kbhse/EnergyMonitor/KiCad/v1.1/images/17747-ESP-WROOM-32__16MB__ESP32_WiFi-BT-BLE_MCU_Module-01.jpg

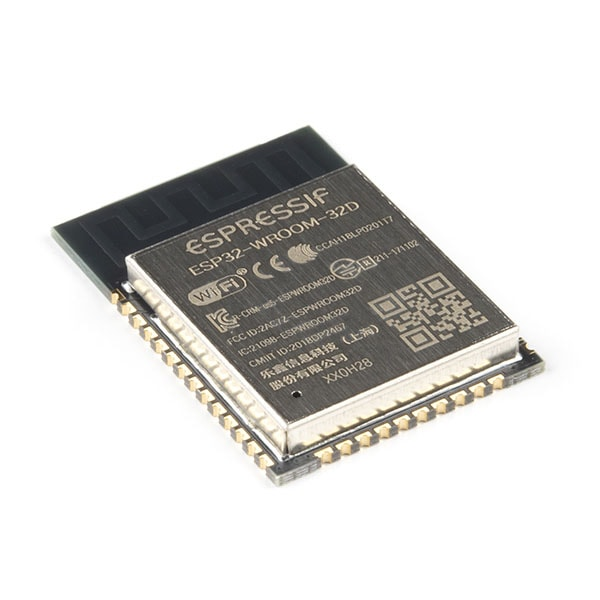
KiCad/v1.1/images/17747-ESP-WROOM-32__16MB__ESP32_WiFi-BT-BLE_MCU_Module-01.jpg
