kbhse/EnergyMonitor/KiCad/v1.1/images/ESP32_D1_MINI Footprint.PNG

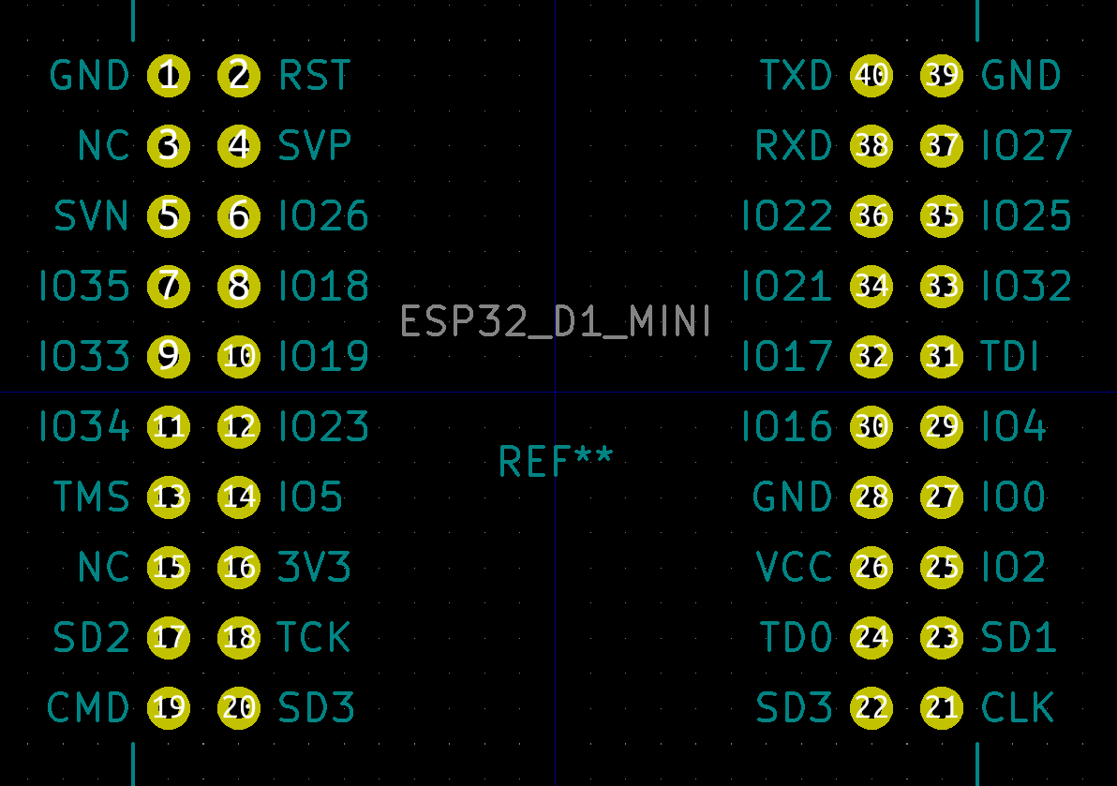
KiCad/v1.1/images/ESP32_D1_MINI Footprint.PNG
