kbhse/EnergyMonitor/Solidworks/images/case v01.png

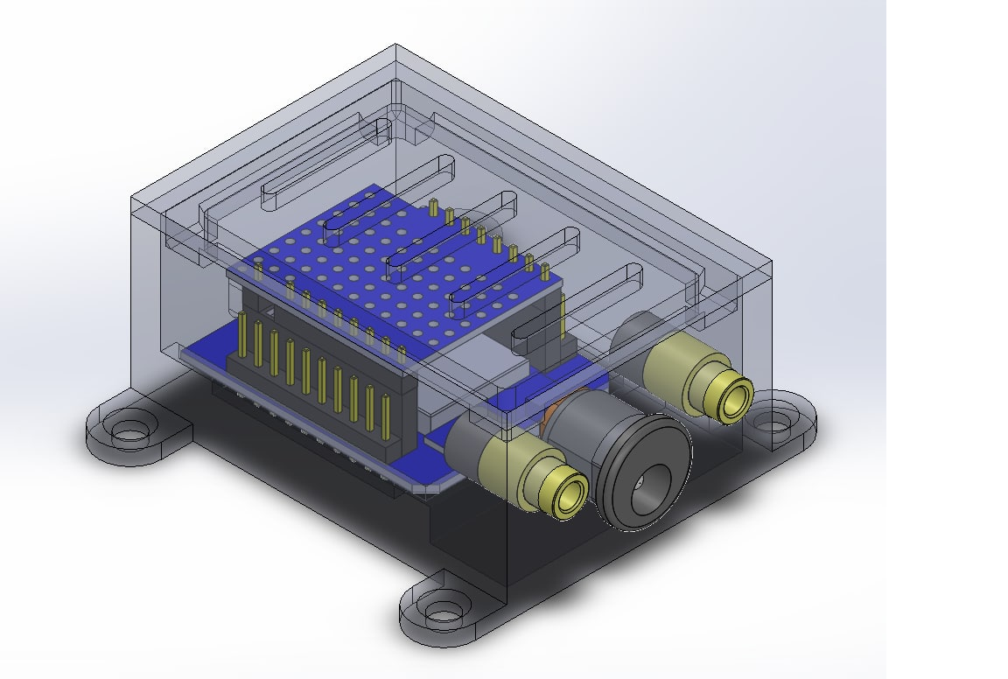
Solidworks/images/case v01.png
