kbhse/EnergyMonitor/Solidworks/images/EnergyMonitor Case v1.2 transparent top.PNG

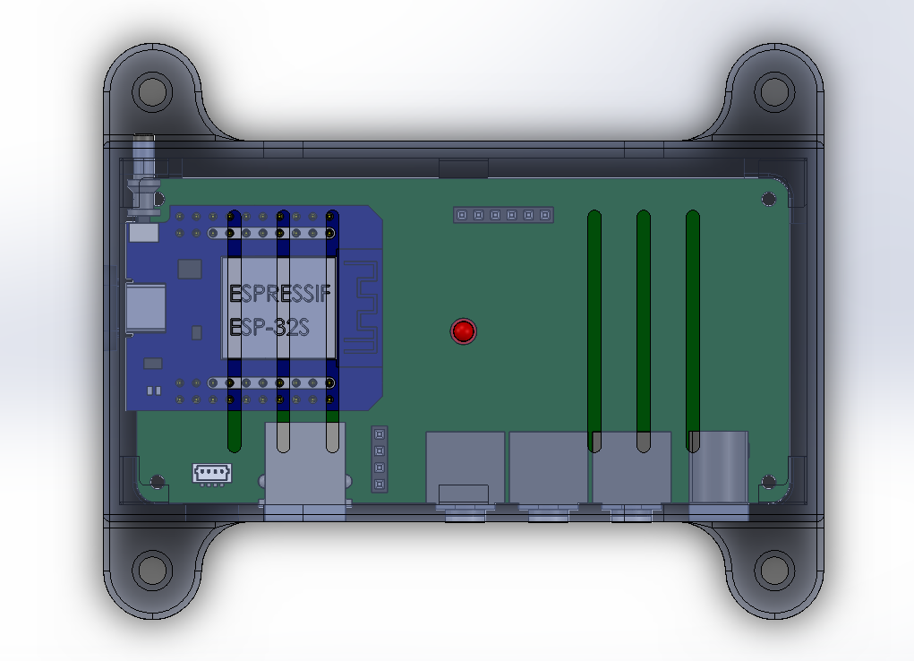
Solidworks/images/EnergyMonitor Case v1.2 transparent top.PNG
