kbhse/EnergyMonitor/Solidworks/images/EnergyMonitor Case v1.2 transparent.PNG

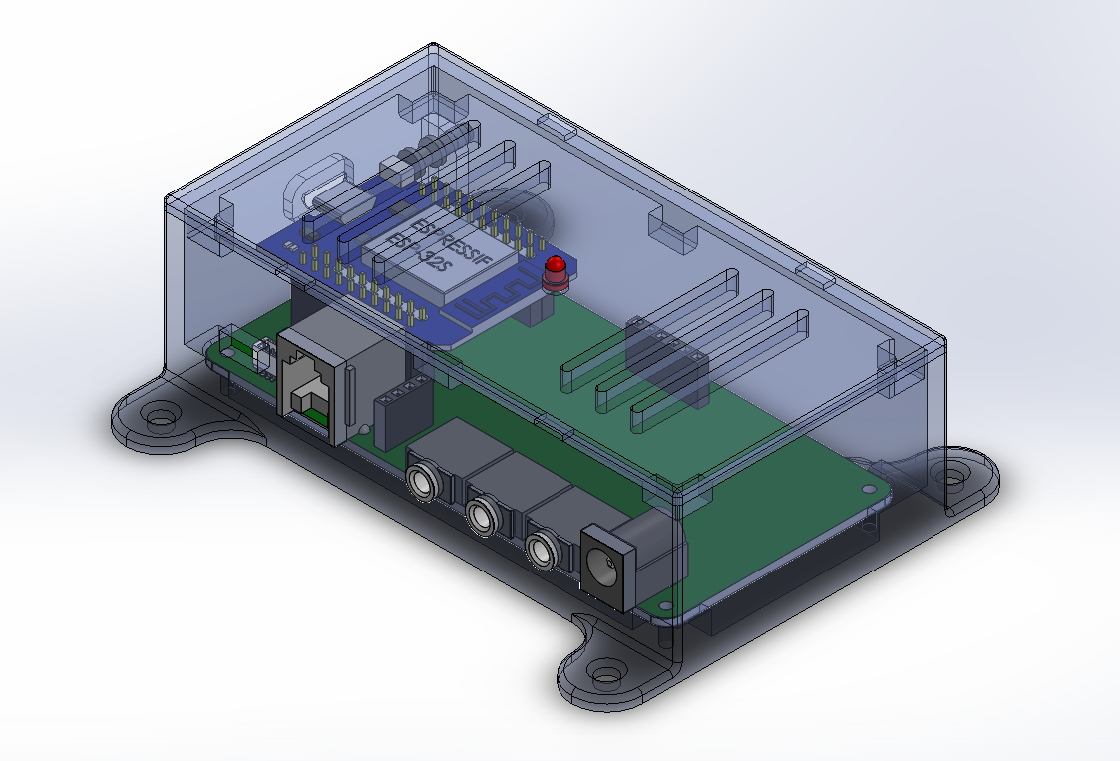
Solidworks/images/EnergyMonitor Case v1.2 transparent.PNG
