kbhse/EnergyMonitor/Solidworks/header pins 1x10.SLDPRT

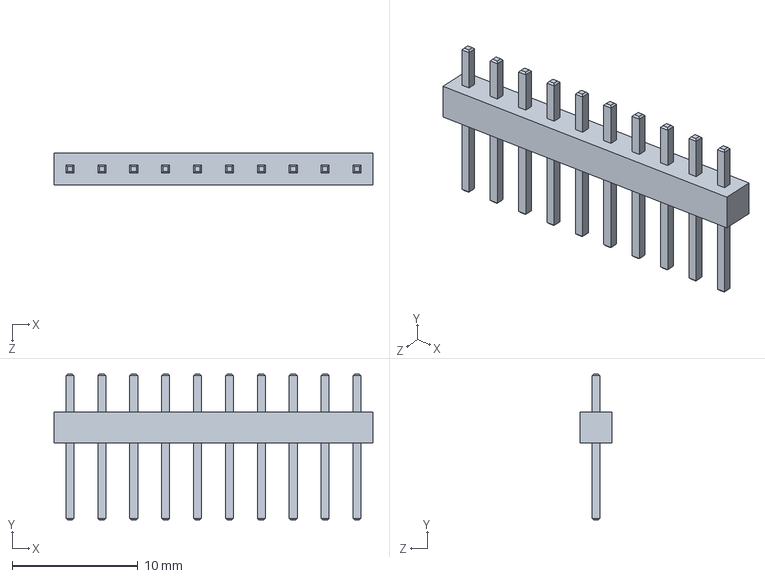
[picture p26: CAD file, 2021-09-27]
Solidworks/header pins 1x10.SLDPRT
25.4 x 11.6 x 2.54 mm
