kbhse/EnergyMonitor/Solidworks/ESP32 D1 mini.STEP

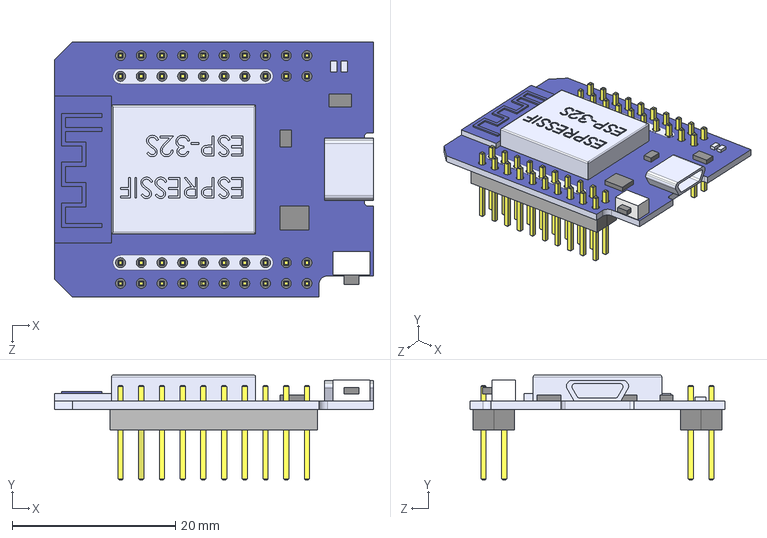
[picture p27: CAD file, 2021-09-27]
Solidworks/ESP32 D1 mini.STEP
39.1 x 12.8 x 31.3 mm
ESP32 D1 mini
header pins 1x10 x 4
