kbhse/EnergyMonitor/Solidworks/EnergyMonitor v1.0.SLDASM

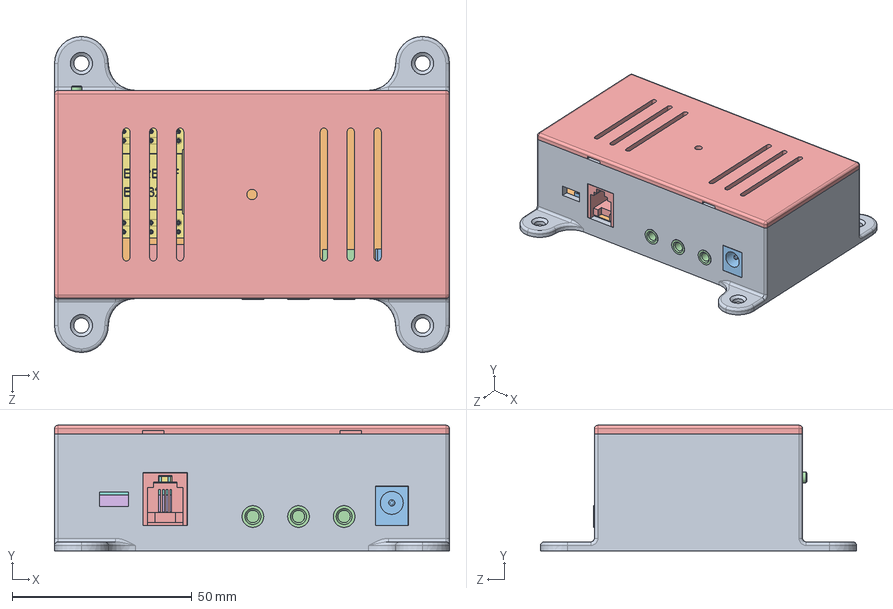
[picture p28: CAD file, 2021-10-03, an earlier design]
Solidworks/EnergyMonitor v1.0.SLDASM
110.0 x 35.0 x 88.0 mm
EnergyMonitor Case v1.0
pcb_v1.0
5.5x2.1mm 3P DC Power Jack PCB Mount Female Socket
PCB Mount 3.5mm 5 Pin Socket x 3
RJ9 4P4C (#C026)
header sockets 1x10 x 4
ESP32 D1 mini
header pins 1x10 x 4
header sockets 1x6
header sockets 1x4
JST_SH_BM04B_SRDD_TB_04x1.00mm
reset pin
EnergyMonitor Case top v1.1
