kbhse/EnergyMonitor/PlatformIO/ESP32_WiFi_MQTT_EnergyMonitor/src/credentials.h

/* credentials.h */

#ifndef CREDENTIALS_H   /* include guards */
#define CREDENTIALS_H

    // ------------------------------------------------------------------
    // WiFi

    const char* ssid = "<SSID>";
    const char* ssidPassword = "<PASSWORD>";

    // ------------------------------------------------------------------
    // MQTT

    const char* mqttServer = "<IP_ADDRESS>";
    const char* mqttUser = "<MQTT_USERNAME>";
    const char* mqttPassword = "<PASSWORD>";

    const int mqttPort = 1883;

   // ------------------------------------------------------------------

    #endif // CREDENTIALS_H
